richardhawthorn/Wifi7Segment/images/DSC_4937.JPG

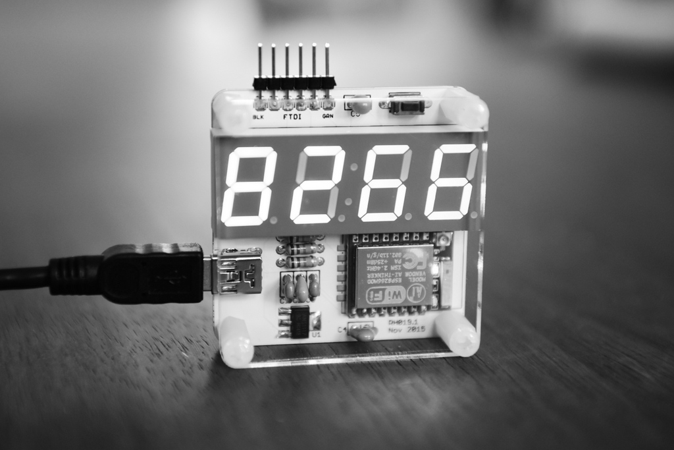
images/DSC_4937.JPG
