richardhawthorn/Wifi7Segment/images/DSC_4956.JPG

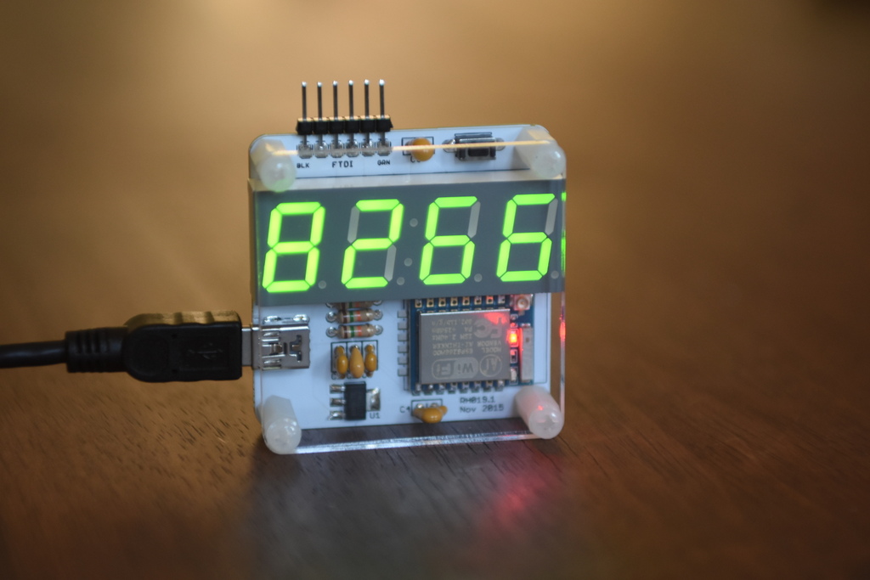
images/DSC_4956.JPG
